dpmj/Master_Thesis_LoRa_Gateway_CubeSat_Payload_hardware/egse/outputs/Drawings/egse.png

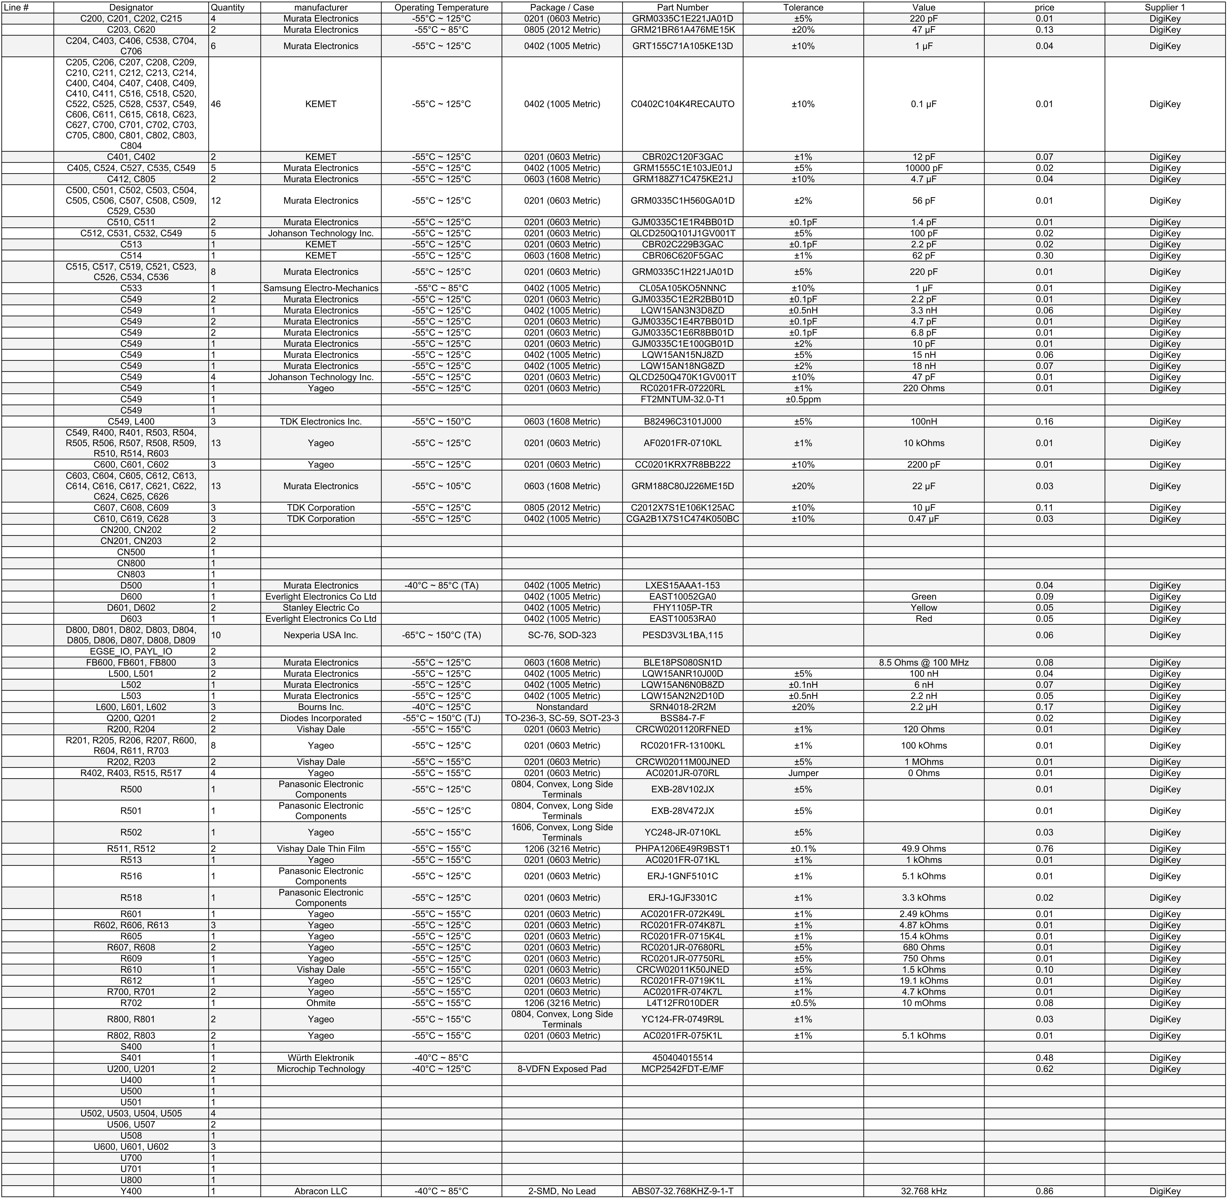
egse/outputs/Drawings/egse.png
