dpmj/Master_Thesis_LoRa_Gateway_CubeSat_Payload_hardware/lora_gw_som/outputs/Drawings/bom.png

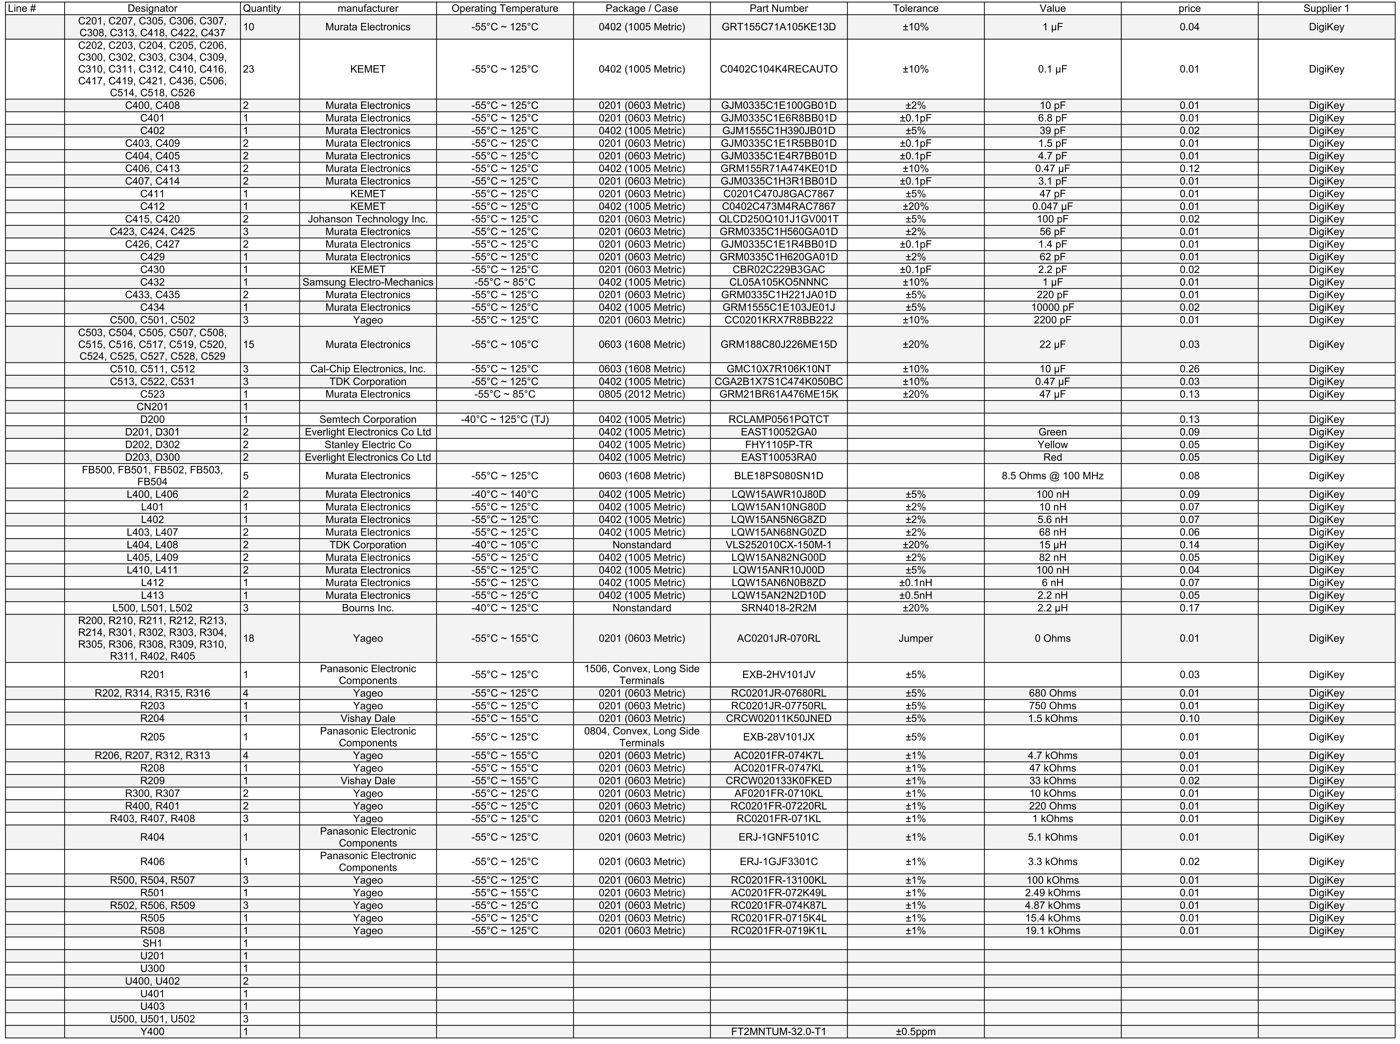
lora_gw_som/outputs/Drawings/bom.png
