dpmj/Master_Thesis_LoRa_Gateway_CubeSat_Payload_hardware/estigia_lora_comms/library-common/models/SMA/sma_straight.stp

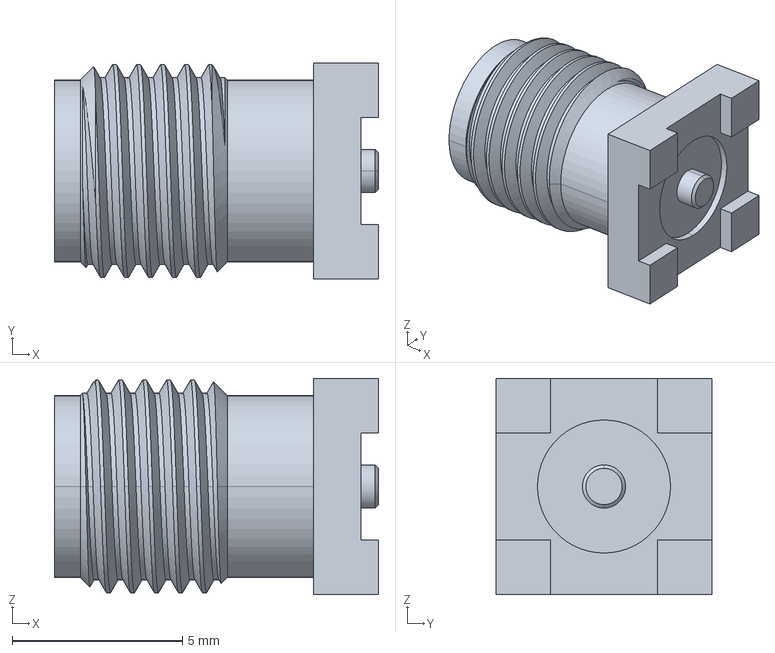
[picture p18: CAD file, 2025-09-22]
estigia_lora_comms/library-common/models/SMA/sma_straight.stp
9.53 x 6.35 x 6.35 mm
