dpmj/Master_Thesis_LoRa_Gateway_CubeSat_Payload_hardware/estigia_lora_comms/library-common/models/SOT-23-8-INA232BIDDFR/INA232BIDDFR.stp

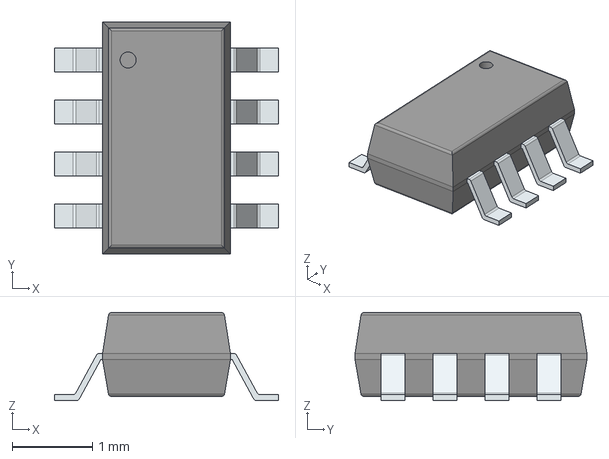
[picture p19: CAD file, 2025-09-22]
estigia_lora_comms/library-common/models/SOT-23-8-INA232BIDDFR/INA232BIDDFR.stp
2.80 x 2.90 x 1.10 mm
PinsArrayLR
