dpmj/Master_Thesis_LoRa_Gateway_CubeSat_Payload_hardware/estigia_lora_comms/library-common/models/Standoffs/standoff_M3_15mm_hex.step

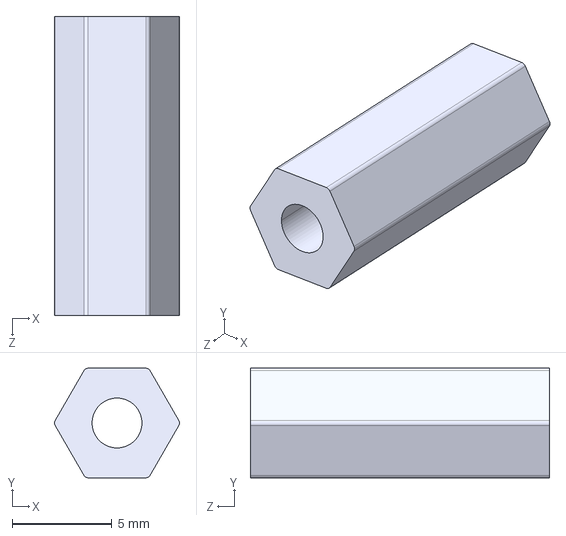
[picture p20: CAD file, 2025-09-22]
estigia_lora_comms/library-common/models/Standoffs/standoff_M3_15mm_hex.step
6.27 x 5.50 x 15.0 mm
