dpmj/Master_Thesis_LoRa_Gateway_CubeSat_Payload_hardware/estigia_lora_comms/library-common/models/UDFN6-STTS751/UDFN6.step

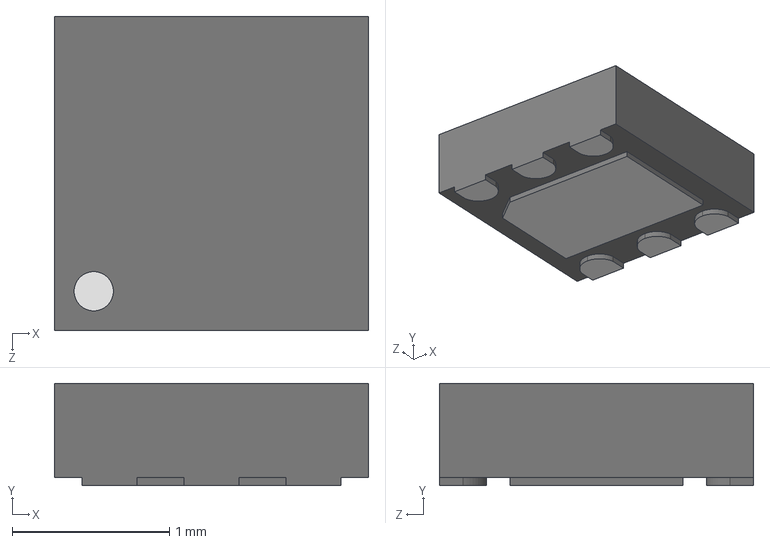
[picture p21: CAD file, 2025-09-22]
estigia_lora_comms/library-common/models/UDFN6-STTS751/UDFN6.step
2.00 x 0.65 x 2.00 mm
