dpmj/Master_Thesis_LoRa_Gateway_CubeSat_Payload_hardware/estigia_lora_comms/library-common/models/USBLC6-2SC6 SOT23-6/USBLC6-2SC6.stp

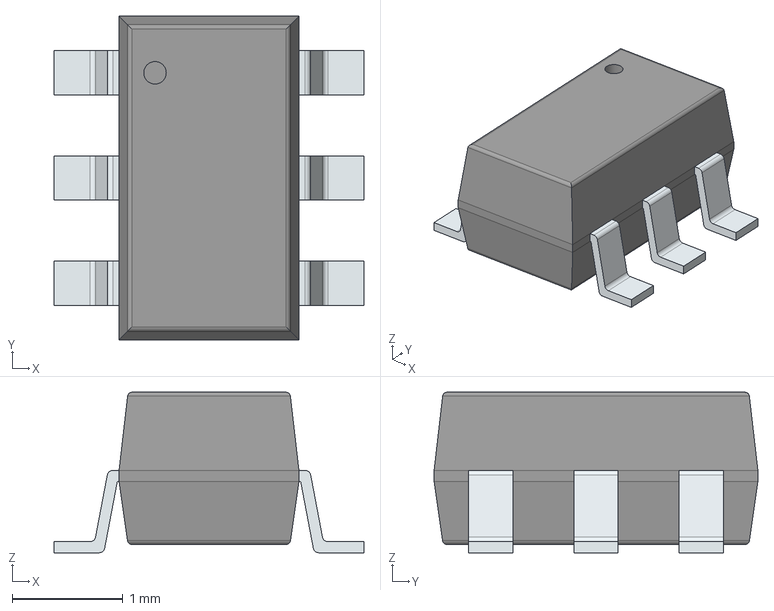
[picture p22: CAD file, 2025-09-22]
estigia_lora_comms/library-common/models/USBLC6-2SC6 SOT23-6/USBLC6-2SC6.stp
2.80 x 2.92 x 1.45 mm
PinsArrayLR
