dpmj/Master_Thesis_LoRa_Gateway_CubeSat_Payload_hardware/estigia_lora_comms/library-common/models/VQFN-HR 10/VQFN-HR-10P.STEP

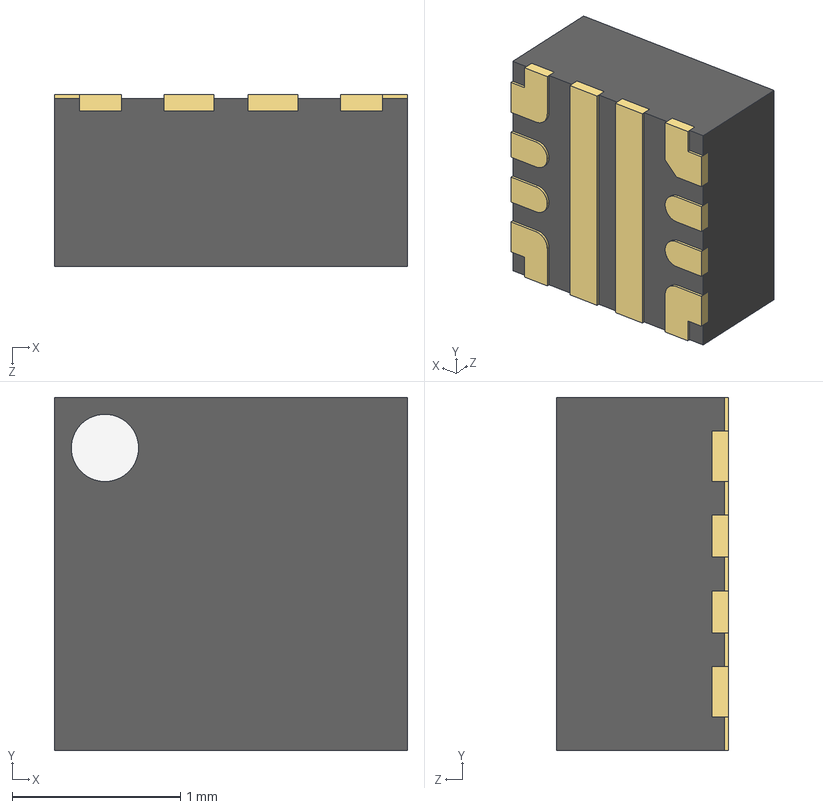
[picture p23: CAD file, 2025-09-22]
estigia_lora_comms/library-common/models/VQFN-HR 10/VQFN-HR-10P.STEP
2.10 x 2.10 x 1.02 mm
