dpmj/Master_Thesis_LoRa_Gateway_CubeSat_Payload_hardware/lora_gw_som/outputs/3D STEP/lora_gw_som_pcb_only.step

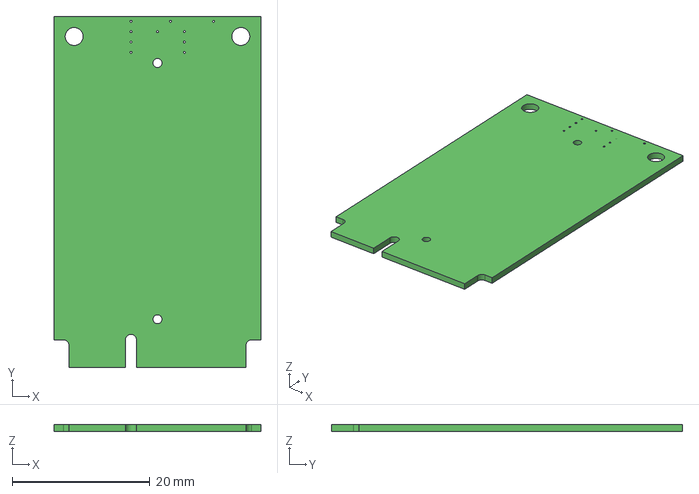
[picture p24: CAD file, 2025-09-22]
lora_gw_som/outputs/3D STEP/lora_gw_som_pcb_only.step
30.0 x 51.0 x 0.976 mm
