dpmj/Master_Thesis_LoRa_Gateway_CubeSat_Payload_hardware/estigia_lora_comms/library-common/models/JPS-2-1N+/Pins.stp.STEP

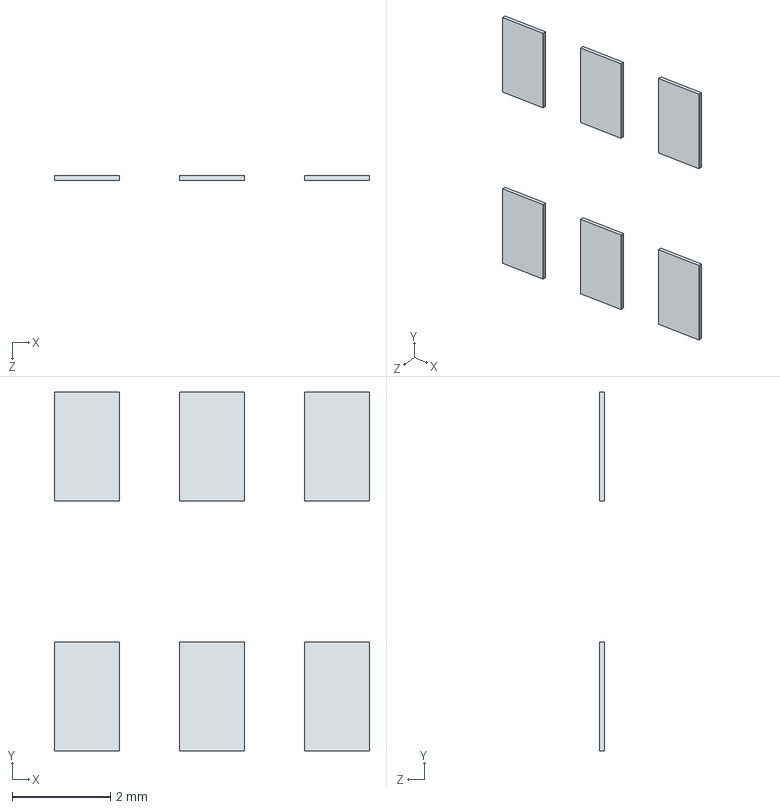
[picture p25: CAD file, 2025-09-22]
estigia_lora_comms/library-common/models/JPS-2-1N+/Pins.stp.STEP
6.40 x 7.29 x 0.1 mm
