dpmj/Master_Thesis_LoRa_Gateway_CubeSat_Payload_hardware/estigia_lora_comms/library-common/models/QFN-28/QFN28-0_5.STEP

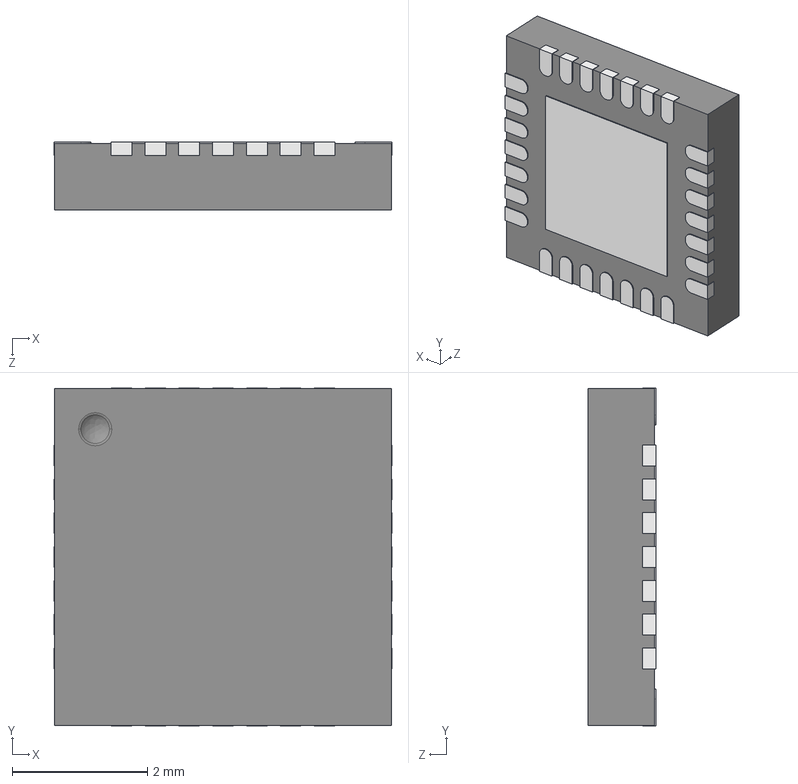
[picture p26: CAD file, 2025-09-22]
estigia_lora_comms/library-common/models/QFN-28/QFN28-0_5.STEP
5.00 x 5.00 x 1.00 mm
