dpmj/Master_Thesis_LoRa_Gateway_CubeSat_Payload_hardware/estigia_lora_comms/library-common/models/SMA/sma_right.stp

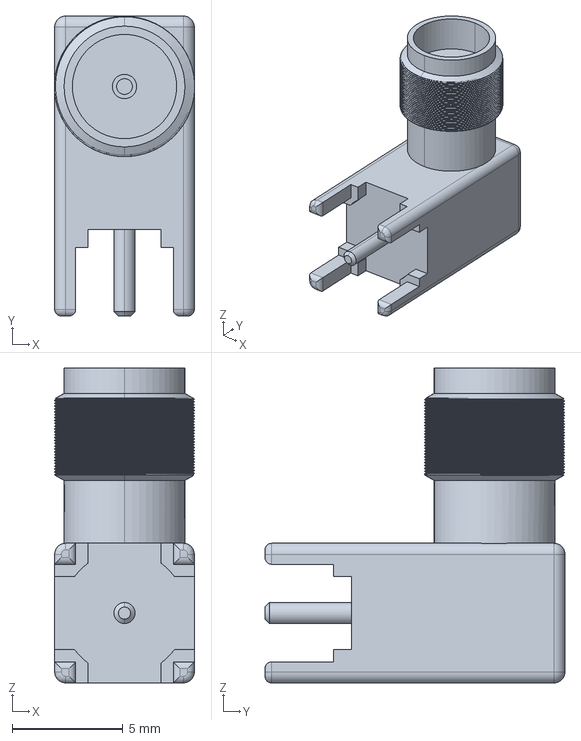
[picture p27: CAD file, 2025-09-22]
estigia_lora_comms/library-common/models/SMA/sma_right.stp
6.33 x 13.5 x 14.2 mm
