dpmj/Master_Thesis_LoRa_Gateway_CubeSat_Payload_hardware/estigia_lora_comms/library-common/models/TXB0104NMN/body.STEP

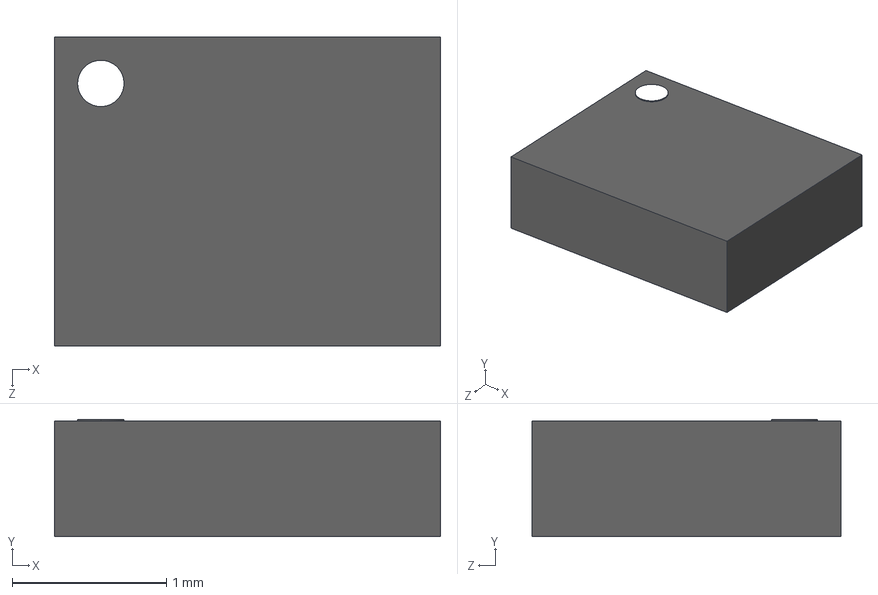
[picture p28: CAD file, 2025-09-22]
estigia_lora_comms/library-common/models/TXB0104NMN/body.STEP
2.50 x 0.76 x 2.00 mm
