dpmj/Master_Thesis_LoRa_Gateway_CubeSat_Payload_hardware/estigia_lora_comms/library-common/models/UDFN6-STTS751/STTS751-0DP3F.stp

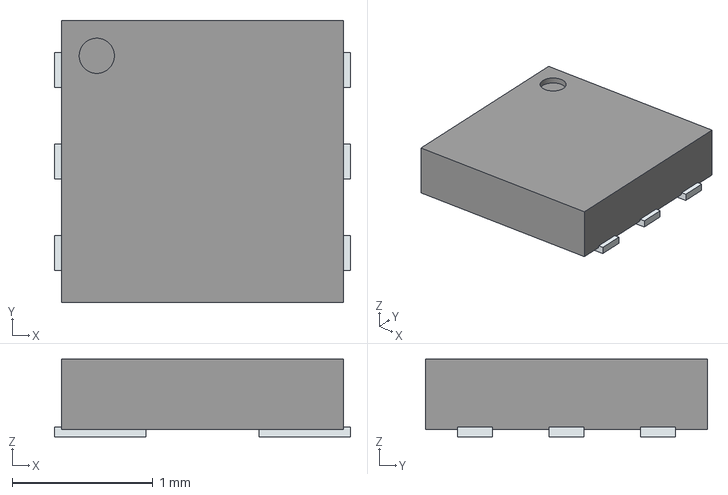
[picture p29: CAD file, 2025-09-22]
estigia_lora_comms/library-common/models/UDFN6-STTS751/STTS751-0DP3F.stp
2.10 x 2.00 x 0.55 mm
PinsArrayLR
