dpmj/Master_Thesis_LoRa_Gateway_CubeSat_Payload_hardware/estigia_lora_comms/library-common/models/JPS-2-1N+/JPS-2-1N+_2.STEP

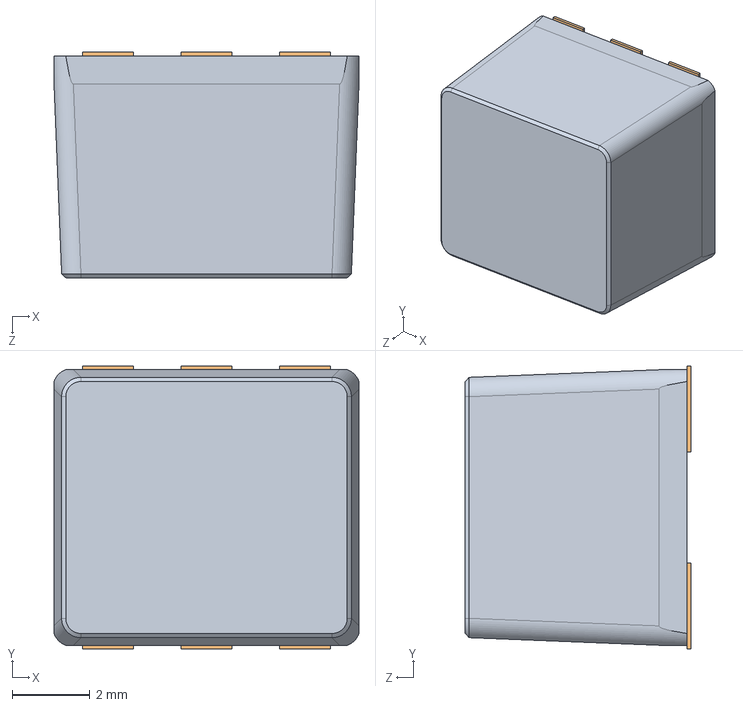
[picture p30: CAD file, 2025-09-22]
estigia_lora_comms/library-common/models/JPS-2-1N+/JPS-2-1N+_2.STEP
7.87 x 7.29 x 5.82 mm
