dpmj/Master_Thesis_LoRa_Gateway_CubeSat_Payload_hardware/estigia_lora_comms/library-common/models/TXB0104NMN/ball.STEP.STEP

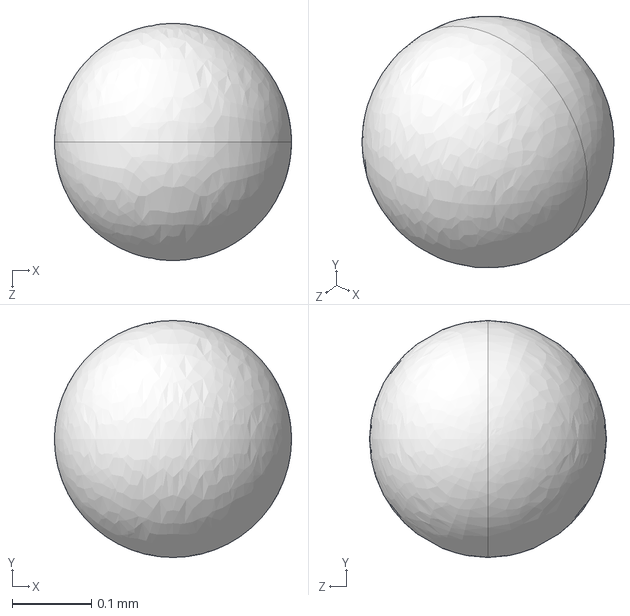
[picture p31: CAD file, 2025-09-22]
estigia_lora_comms/library-common/models/TXB0104NMN/ball.STEP.STEP
0.3 x 0.3 x 0.3 mm
