dpmj/Master_Thesis_LoRa_Gateway_CubeSat_Payload_hardware/estigia_lora_comms/library-common/models/JPS-2-1N+/Body.stp.STEP

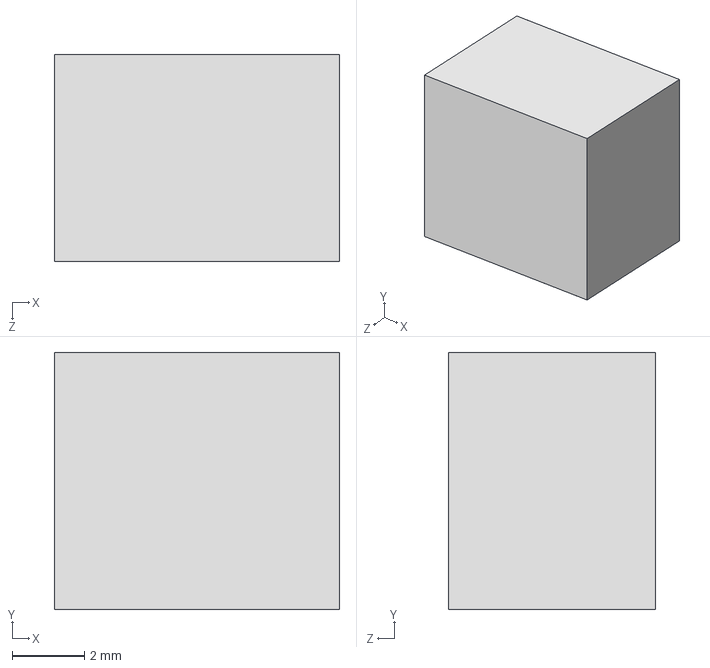
[picture p32: CAD file, 2025-09-22]
estigia_lora_comms/library-common/models/JPS-2-1N+/Body.stp.STEP
7.87 x 7.11 x 5.72 mm
