dpmj/Master_Thesis_LoRa_Gateway_CubeSat_Payload_hardware/estigia_lora_comms/library-common/models/TXB0104NMN/BGA12C50P3X4_156X206X62.STEP

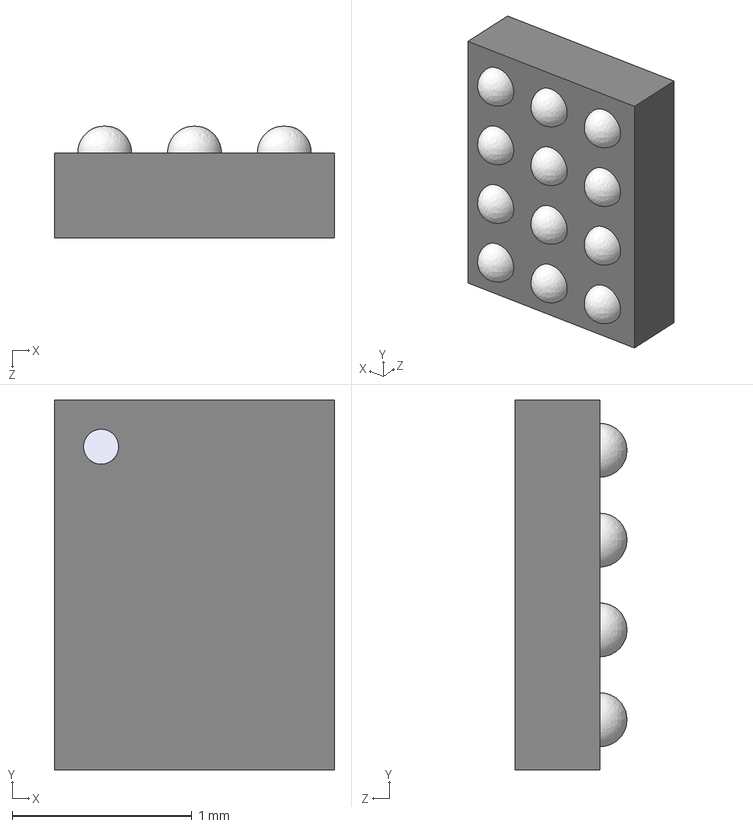
[picture p33: CAD file, 2025-09-22]
estigia_lora_comms/library-common/models/TXB0104NMN/BGA12C50P3X4_156X206X62.STEP
1.56 x 2.06 x 0.625 mm
Open_CASCADE_STEP_translator_6.8_1.1
Open_CASCADE_STEP_translator_6.8_1.2.1
ball x 12
