dpmj/Master_Thesis_LoRa_Gateway_CubeSat_Payload_hardware/estigia_lora_comms/library-common/models/TXB0104NMN/TXB0104NMNR_STEP.STEP

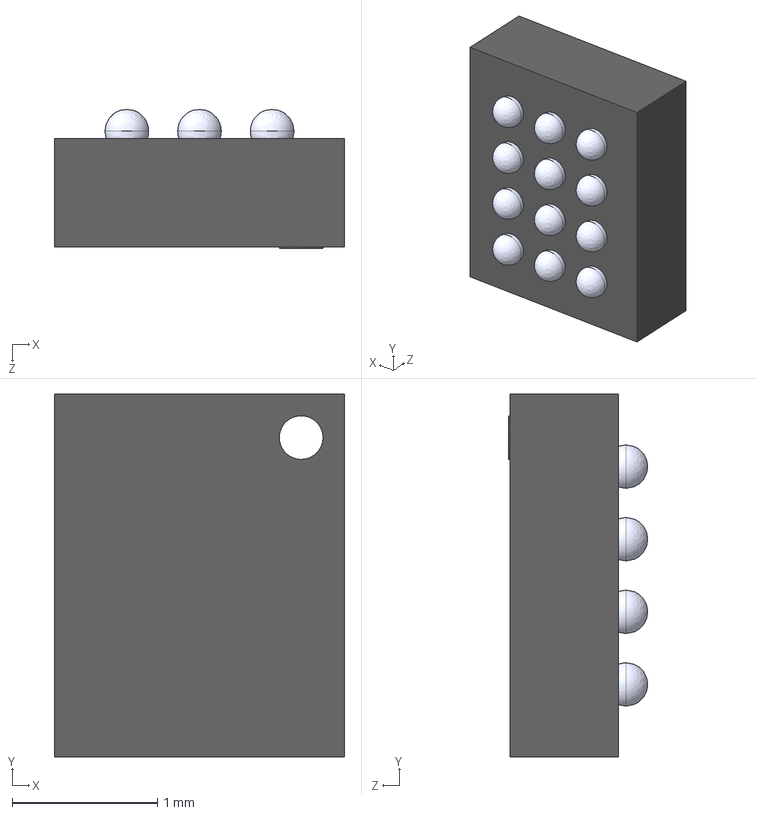
[picture p34: CAD file, 2025-09-22]
estigia_lora_comms/library-common/models/TXB0104NMN/TXB0104NMNR_STEP.STEP
2.00 x 2.50 x 0.96 mm
