dpmj/Master_Thesis_LoRa_Gateway_CubeSat_Payload_hardware/estigia_lora_comms/library-common/models/TXB0104NMN/TXB0104NMNR2.SLDASM

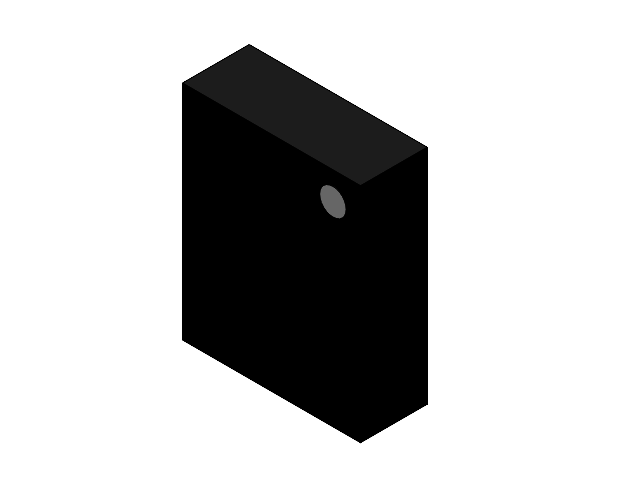
[picture p35: CAD file, 2025-09-22]
estigia_lora_comms/library-common/models/TXB0104NMN/TXB0104NMNR2.SLDASM
ball.STEP.STEP x 12
body_1.STEP
