dpmj/Master_Thesis_LoRa_Gateway_CubeSat_Payload_hardware/estigia_lora_comms/library-common/models/TXB0104NMN/TXB0104NMNR3.SLDASM

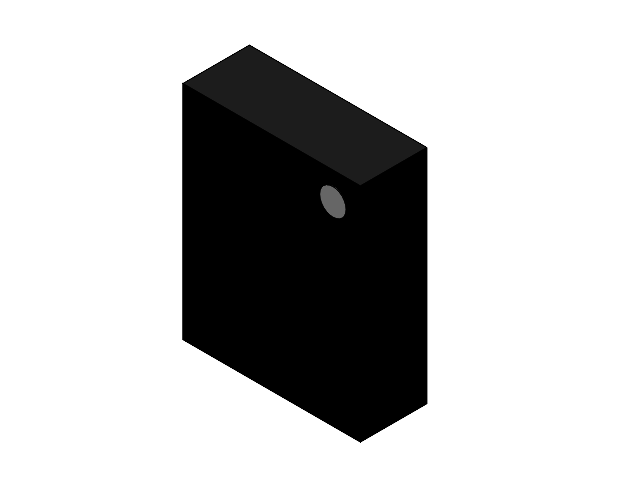
[picture p36: CAD file, 2025-09-22]
estigia_lora_comms/library-common/models/TXB0104NMN/TXB0104NMNR3.SLDASM
ball.STEP.STEP.STEP x 12
body_1.STEP.STEP
